Supermagnum/Flashlight/Screenshot_20191209-161918__01__01.jpg

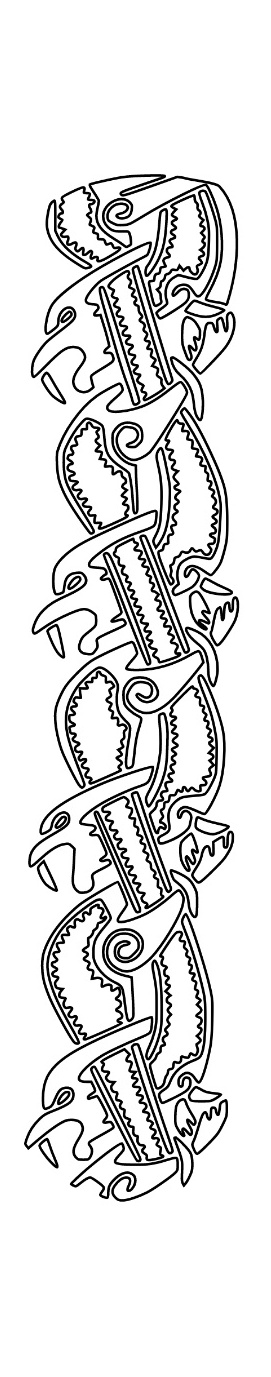
Screenshot_20191209-161918__01__01.jpg
