Supermagnum/Flashlight/Ø32-32650B/32650-n.png

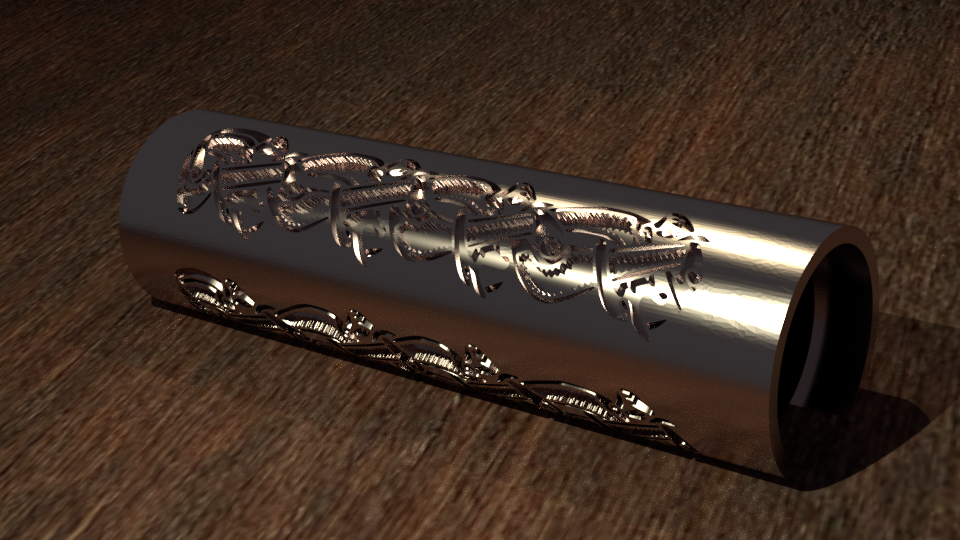
Ø32-32650B/32650-n.png
